houseofthe051010/ESP32-Walkie-Talkie-V2/assets/back-branding-layout.png

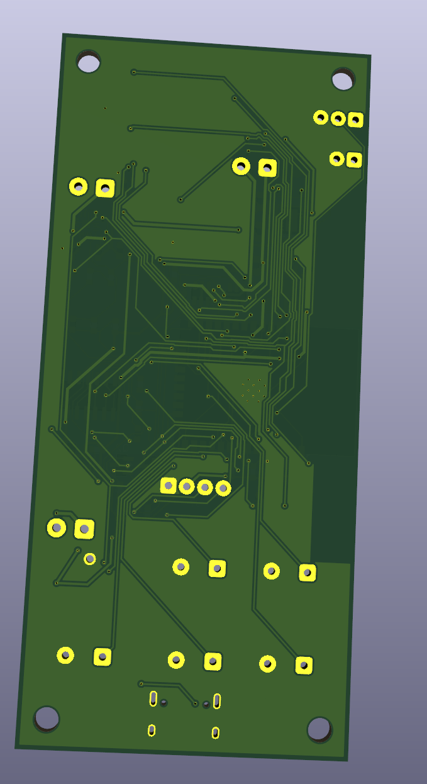
assets/back-branding-layout.png
