houseofthe051010/ESP32-Walkie-Talkie-V2/assets/final-bottom.png

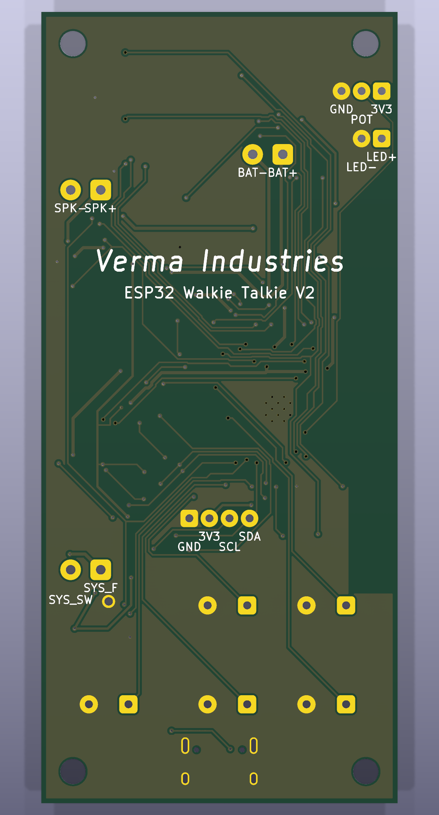
assets/final-bottom.png
