houseofthe051010/ESP32-Walkie-Talkie-V2/assets/final-isometric.png

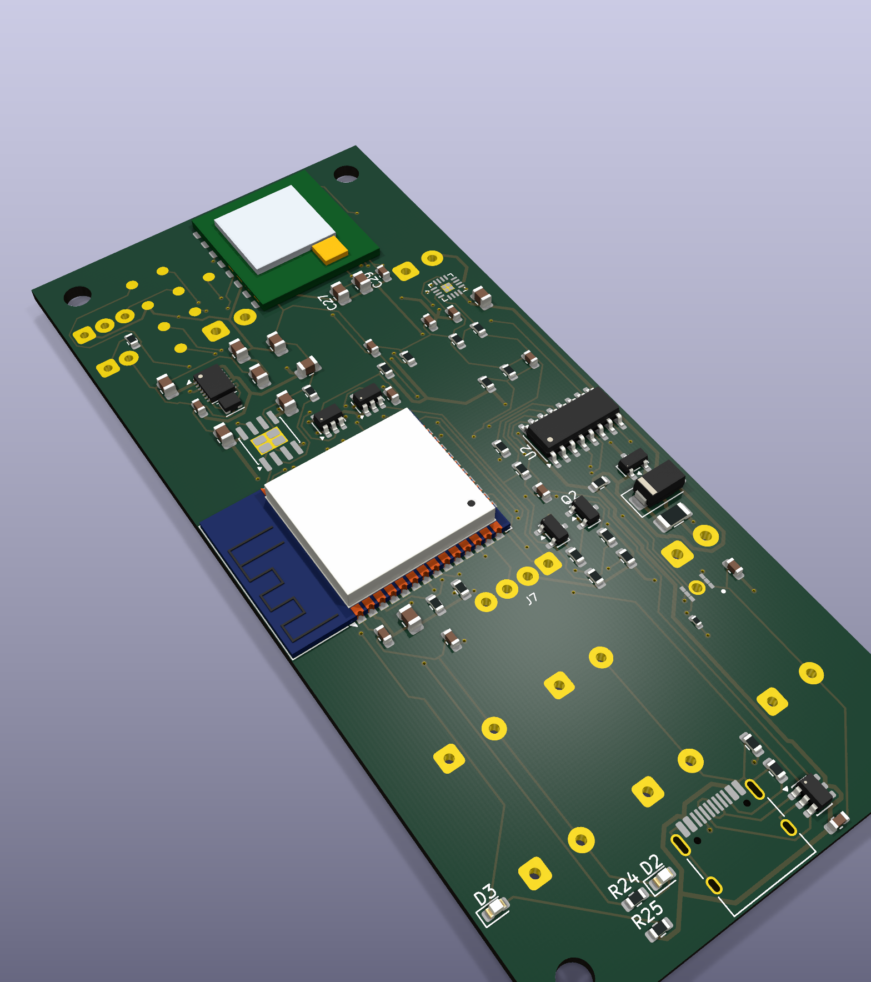
assets/final-isometric.png
