houseofthe051010/ESP32-Walkie-Talkie-V2/assets/final-top.png

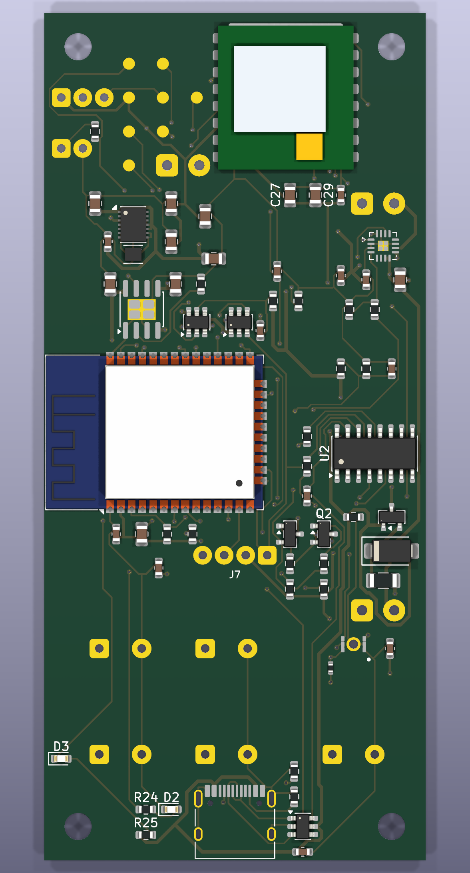
assets/final-top.png
