houseofthe051010/ESP32-Walkie-Talkie-V2/assets/front-copper-audit.png

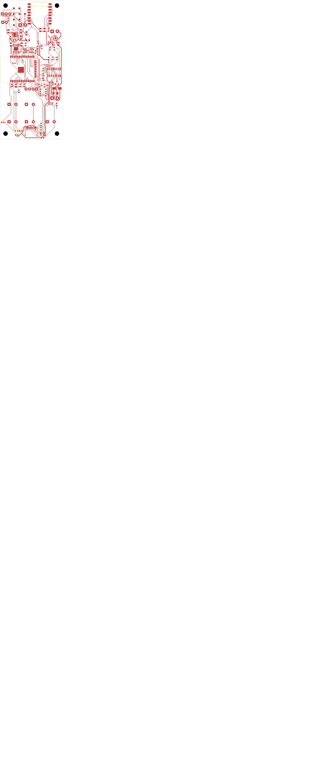
assets/front-copper-audit.png
