houseofthe051010/ESP32-Walkie-Talkie-V2/assets/jlc-esp32-orientation-error.png

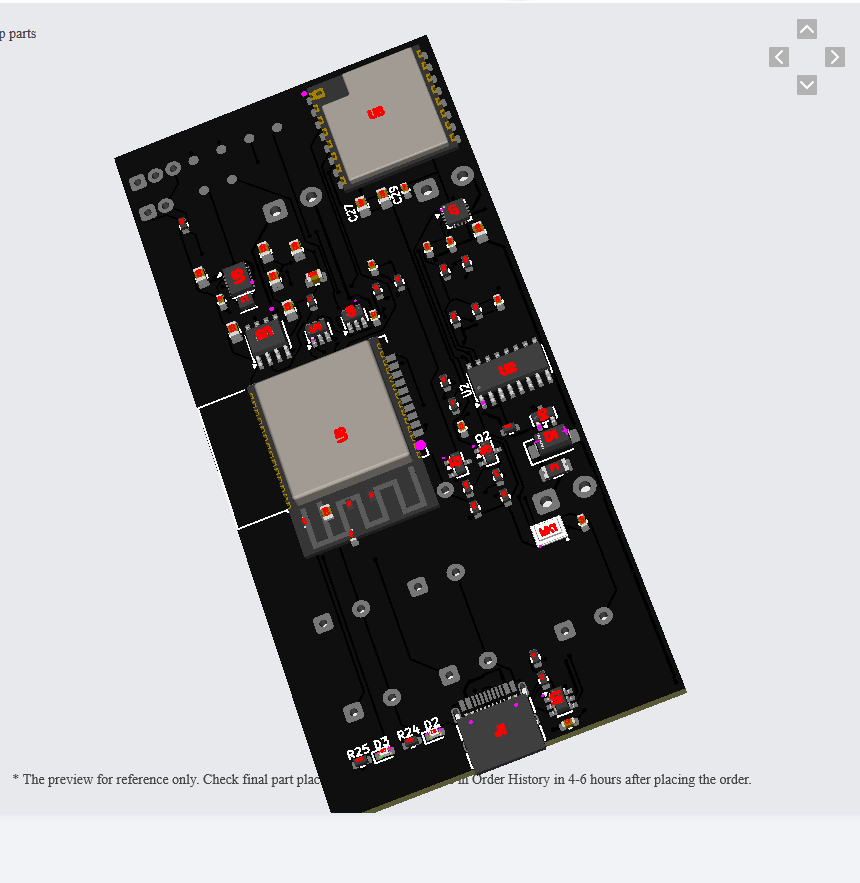
assets/jlc-esp32-orientation-error.png
