houseofthe051010/ESP32-Walkie-Talkie-V2/assets/jlc-price-quote.png

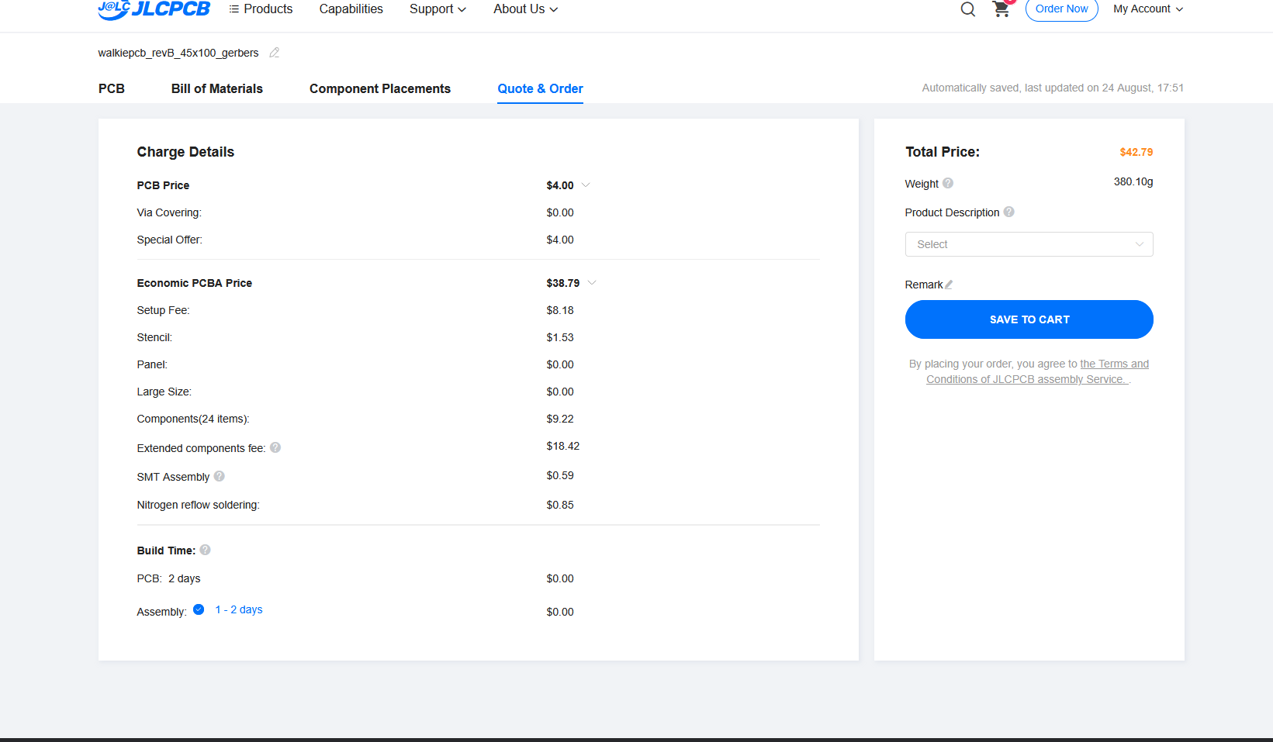
assets/jlc-price-quote.png
