houseofthe051010/ESP32-Walkie-Talkie-V2/assets/jlc-stock-review.png

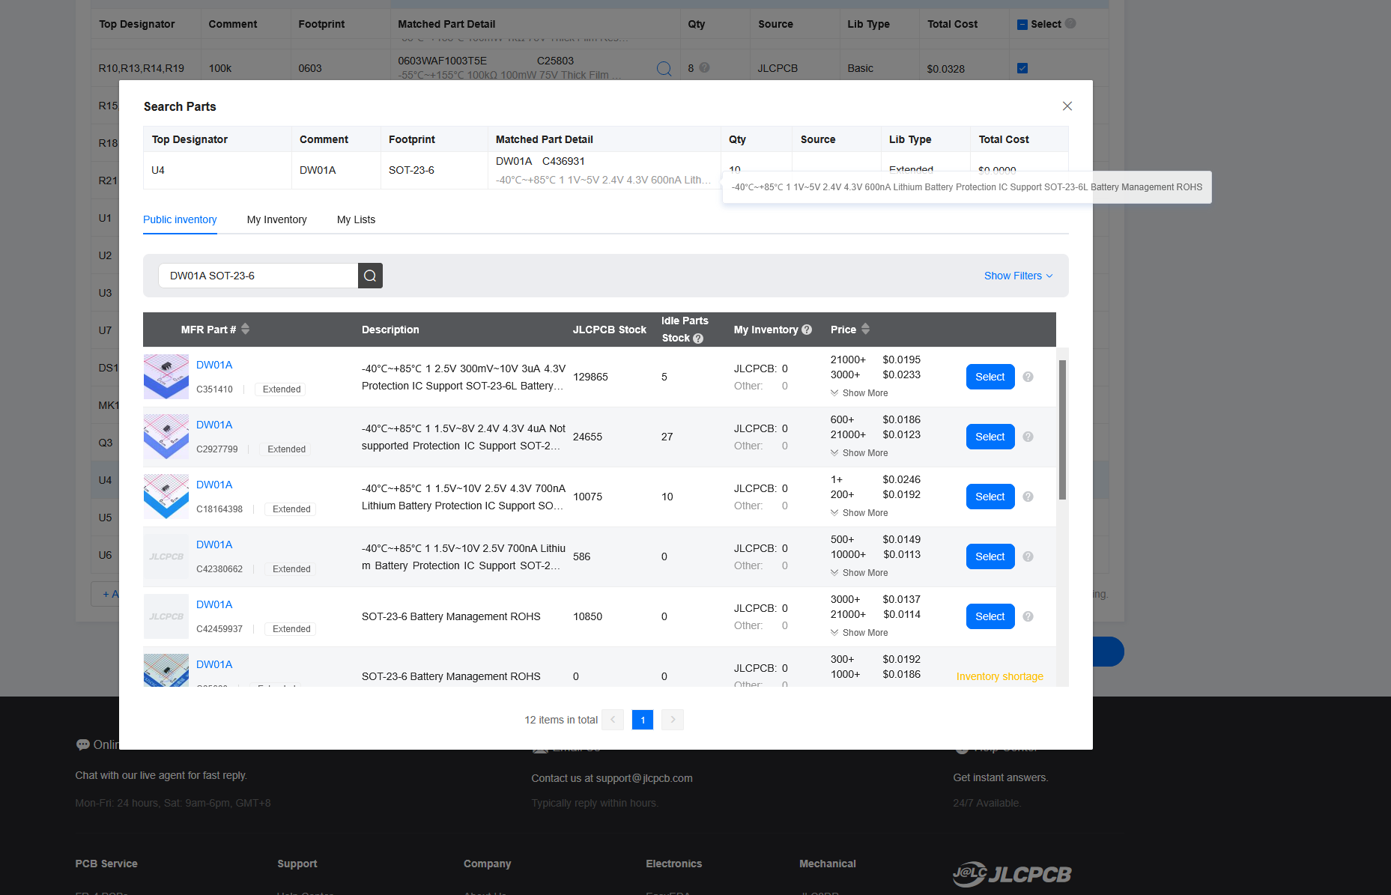
assets/jlc-stock-review.png
