houseofthe051010/ESP32-Walkie-Talkie-V2/assets/middle-layout-review.png

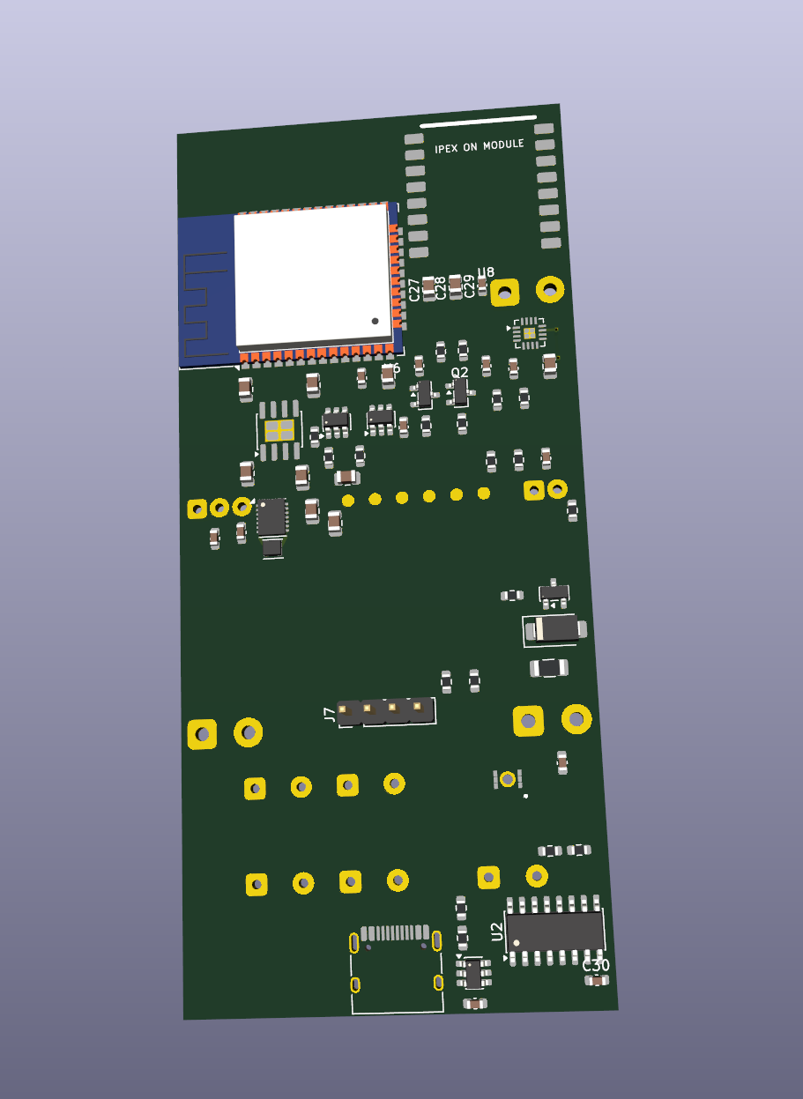
assets/middle-layout-review.png
