houseofthe051010/ESP32-Walkie-Talkie-V2/assets/mounting-layout-review.png

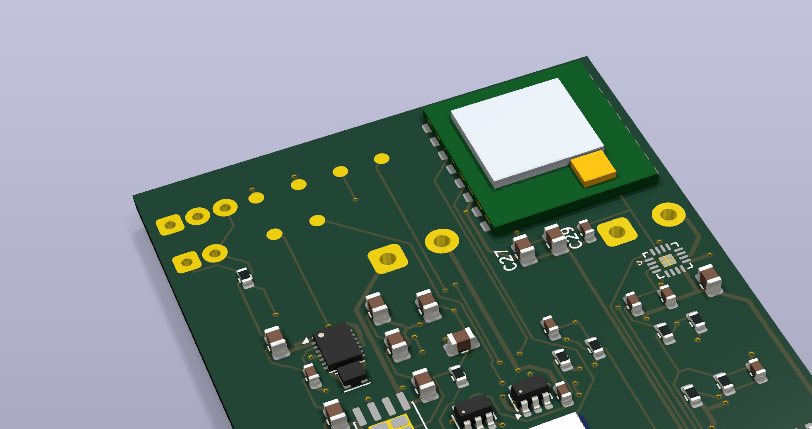
assets/mounting-layout-review.png
