houseofthe051010/ESP32-Walkie-Talkie-V2/assets/oled-header-review.png

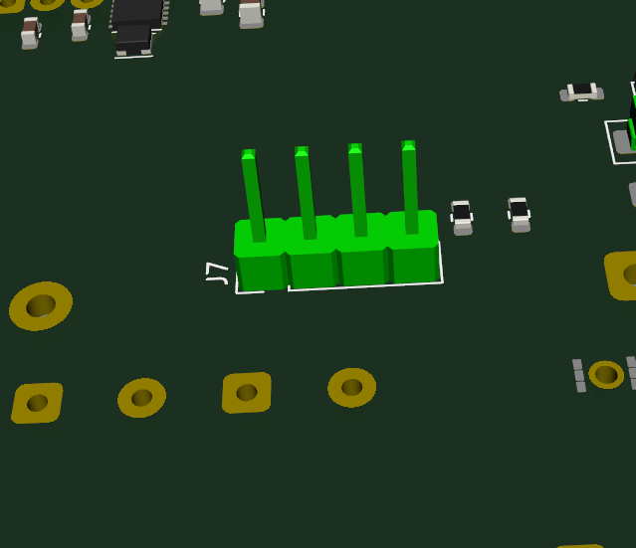
assets/oled-header-review.png
