houseofthe051010/ESP32-Walkie-Talkie-V2/assets/revision-e-bottom.png

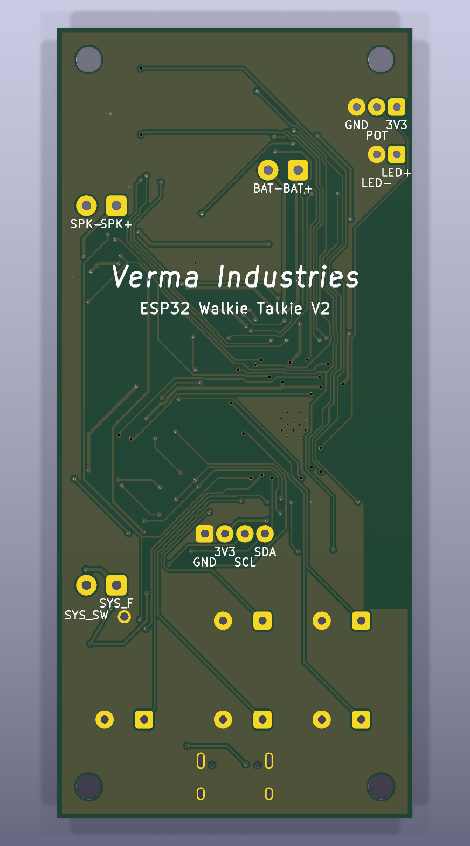
assets/revision-e-bottom.png
