houseofthe051010/ESP32-Walkie-Talkie-V2/assets/revision-e-top.png

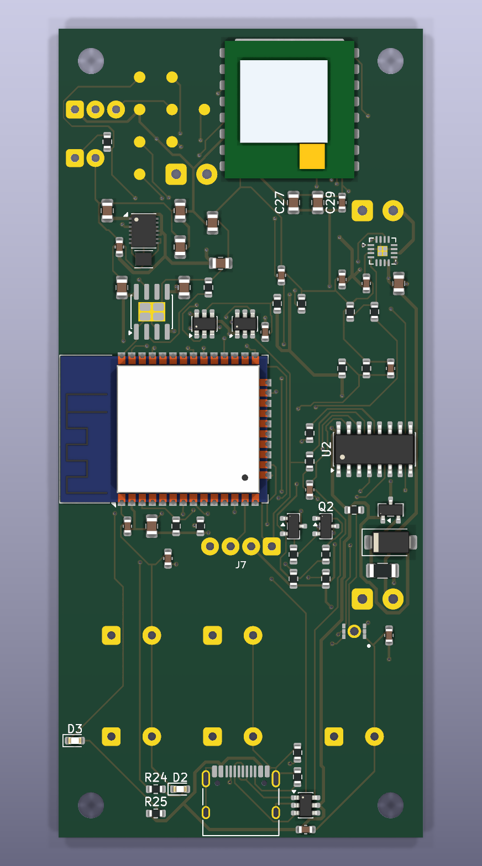
assets/revision-e-top.png
