houseofthe051010/ESP32-Walkie-Talkie-V2/Schematics/KiCad Project/audit-plots/ra01sh_page13.png

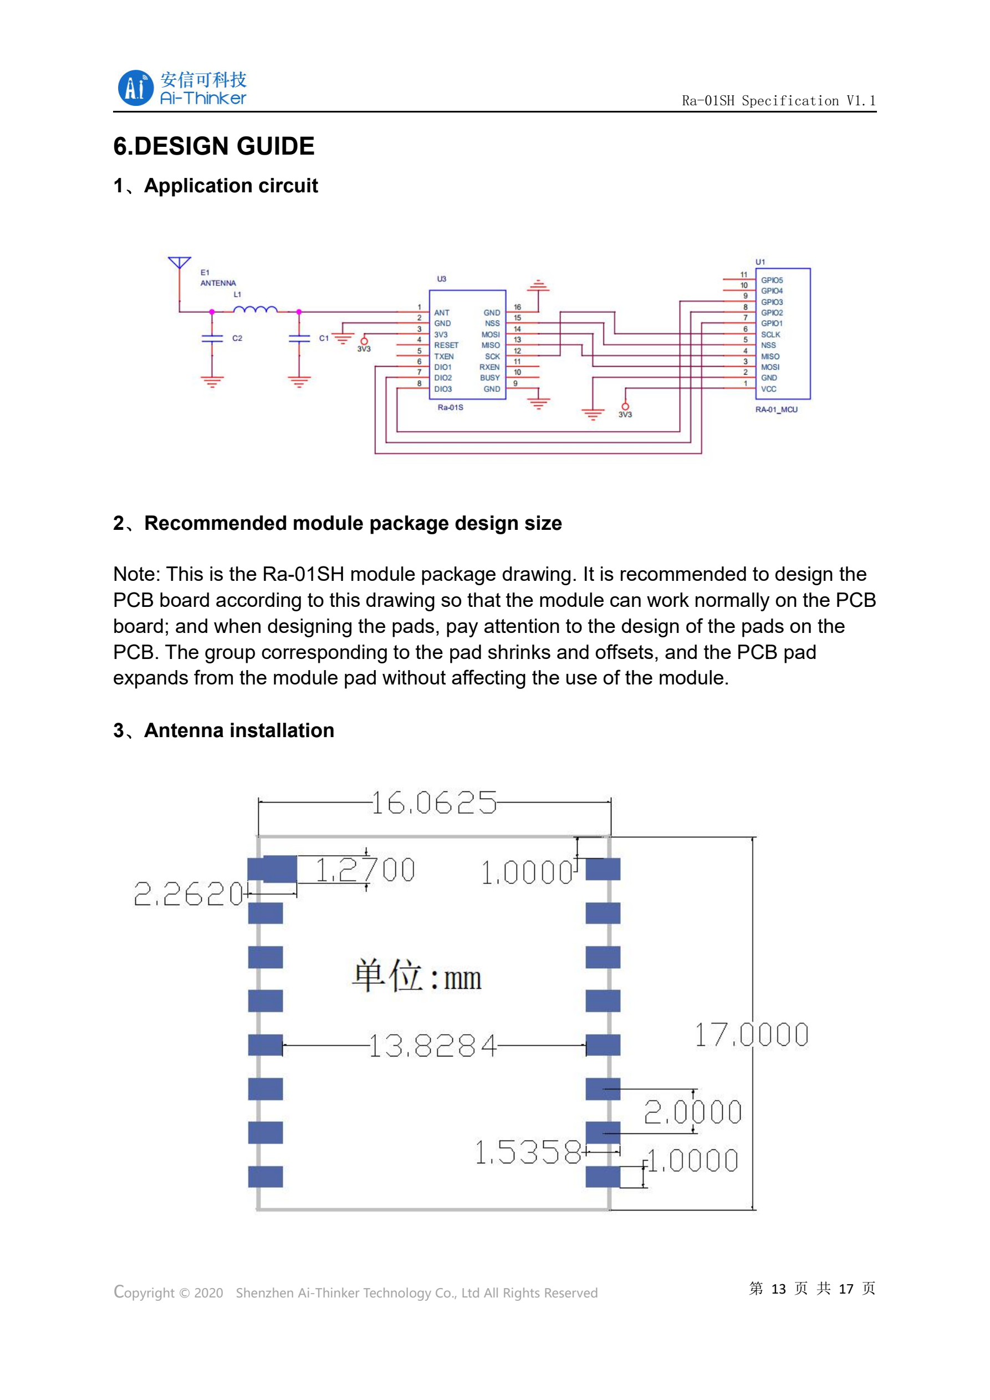
Schematics/KiCad Project/audit-plots/ra01sh_page13.png
