houseofthe051010/ESP32-Walkie-Talkie-V2/assets/jlc-cost-before-esp32.png

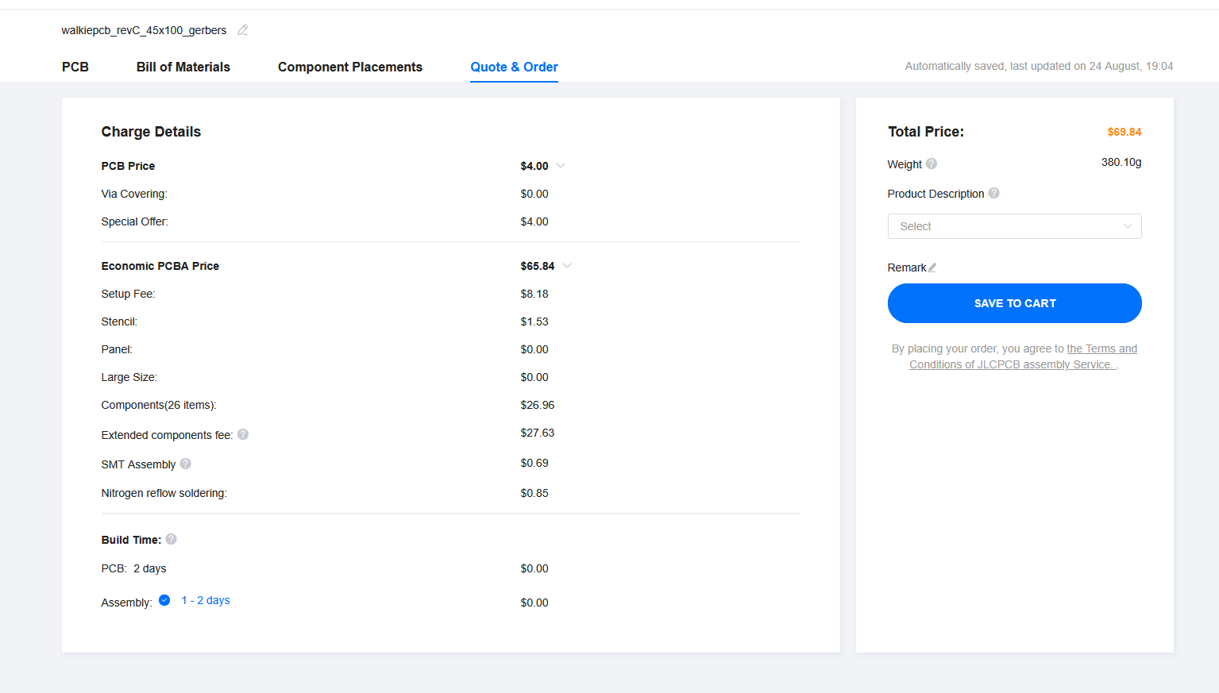
assets/jlc-cost-before-esp32.png
